Gee-Arr-Tee/USB-MIDI-Organ-Conversion-With-Arduino-Leonardo/res/HowTo_Connect_Baldwin_711_Key_Contacts/Baldwin_711_Key_Contact_Board_to_Shift_Registers.gif

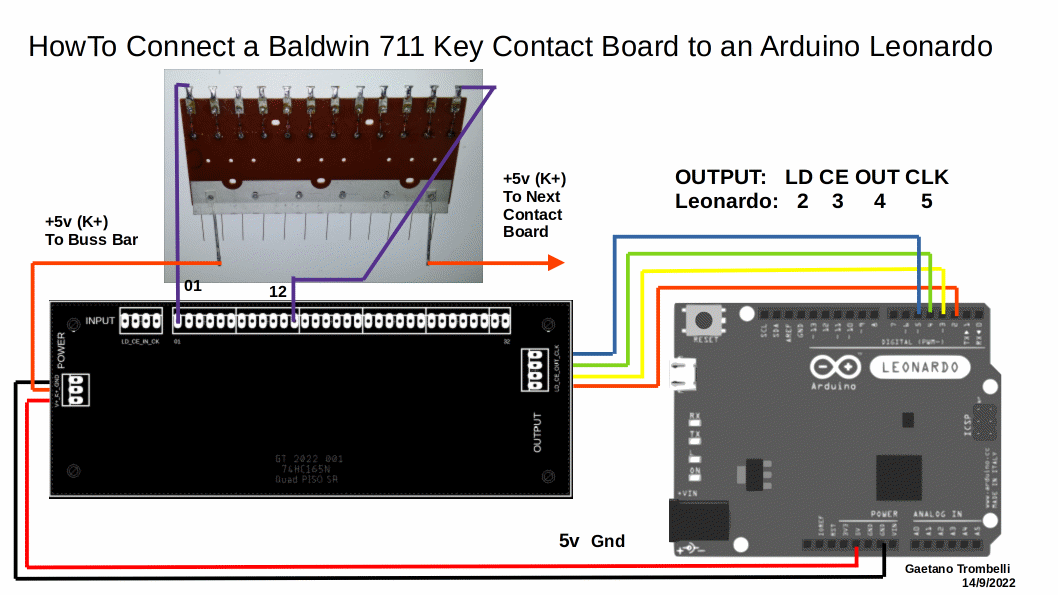
res/HowTo_Connect_Baldwin_711_Key_Contacts/Baldwin_711_Key_Contact_Board_to_Shift_Registers.gif
