Gee-Arr-Tee/USB-MIDI-Organ-Conversion-With-Arduino-Leonardo/res/HowTo_Connect_Baldwin_711_Key_Contacts/Baldwin_711_Key_Contacts_Modification_1of3.gif

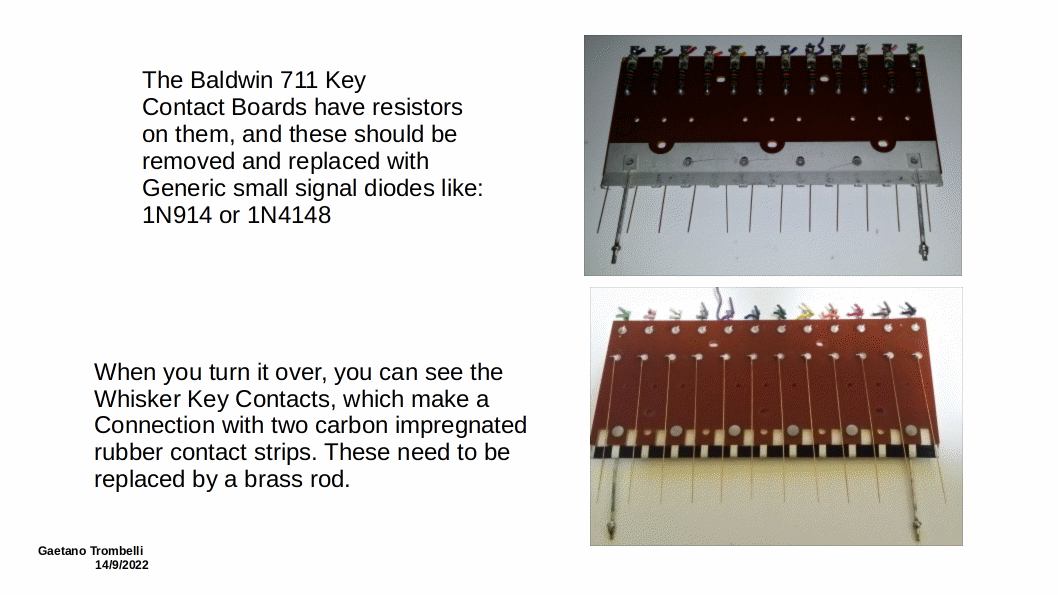
res/HowTo_Connect_Baldwin_711_Key_Contacts/Baldwin_711_Key_Contacts_Modification_1of3.gif
