Gee-Arr-Tee/USB-MIDI-Organ-Conversion-With-Arduino-Leonardo/res/HowTo_Use_The_ShiftRegister_Boards/HowTo_Connect_to_Organ_Buss_Bar.jpg

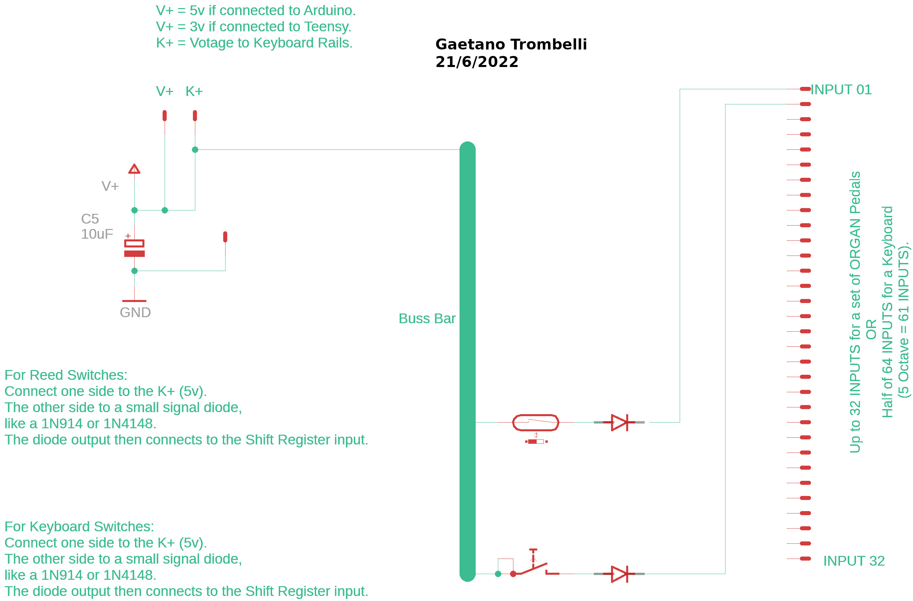
res/HowTo_Use_The_ShiftRegister_Boards/HowTo_Connect_to_Organ_Buss_Bar.jpg
