Gee-Arr-Tee/USB-MIDI-Organ-Conversion-With-Arduino-Leonardo/res/HowTo_Use_The_ShiftRegister_Boards/Potentiometer_with_Jitter_Correction.gif

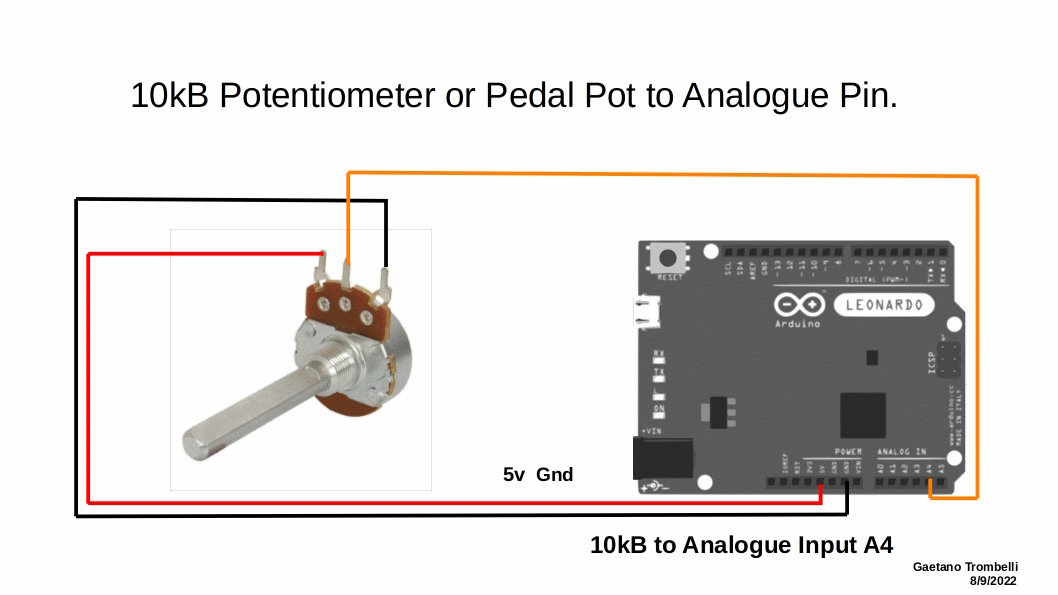
res/HowTo_Use_The_ShiftRegister_Boards/Potentiometer_with_Jitter_Correction.gif
