Gee-Arr-Tee/USB-MIDI-Organ-Conversion-With-Arduino-Leonardo/res/Schematic_and_PCB_Images_and_BOM/PCB_Build_Of_Materials.gif

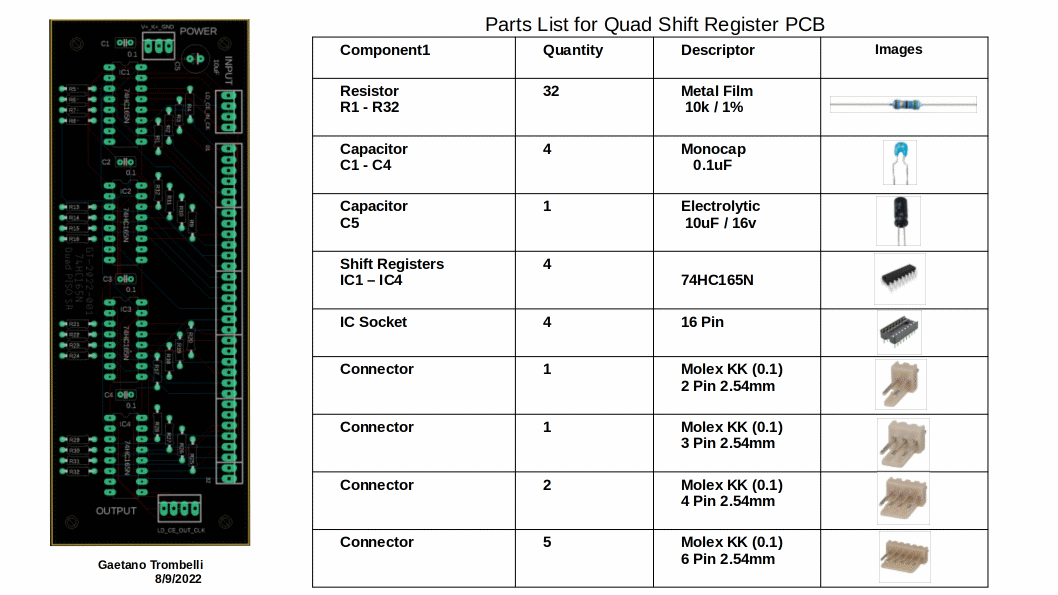
res/Schematic_and_PCB_Images_and_BOM/PCB_Build_Of_Materials.gif
